TarefasUFSC/Sunchaser-Solar_Charging_System/Documentação/Diagramas/alto_nivel_comentado.jpg

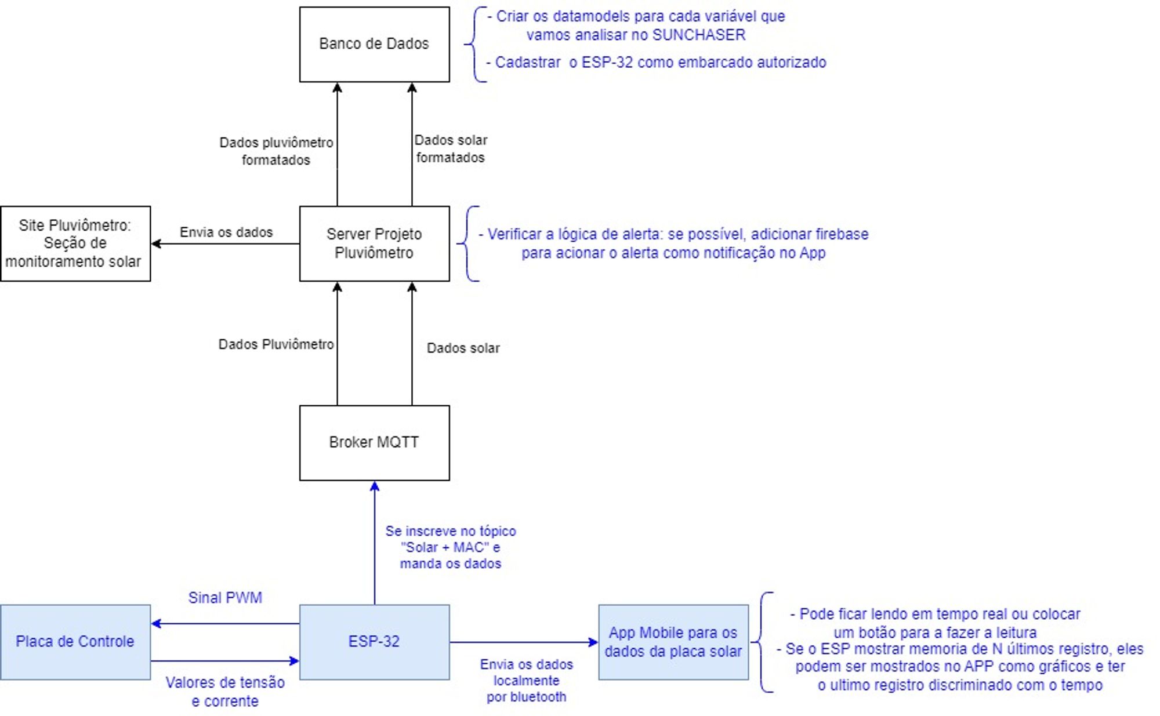
Documentação/Diagramas/alto_nivel_comentado.jpg
