TarefasUFSC/Sunchaser-Solar_Charging_System/Documentação/Diagramas/circuito_eletrico_reguladores.png

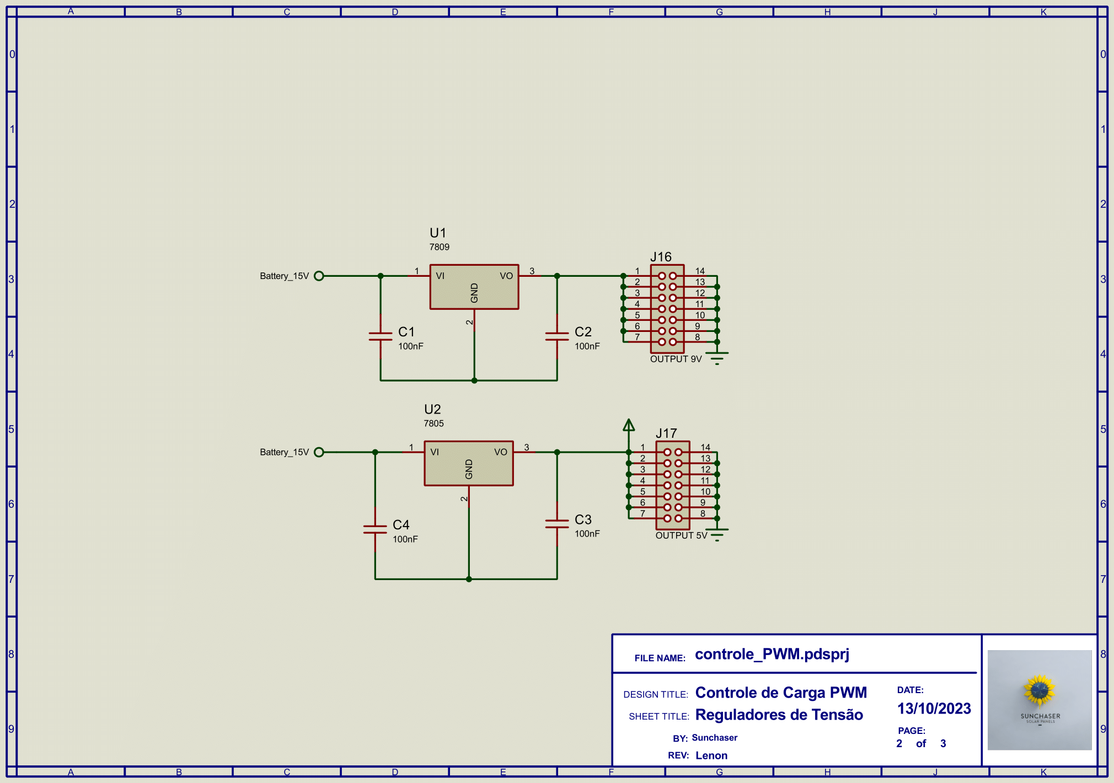
Documentação/Diagramas/circuito_eletrico_reguladores.png
