TarefasUFSC/Sunchaser-Solar_Charging_System/Documentação/Diagramas/circuito_eletrico_sensores.png

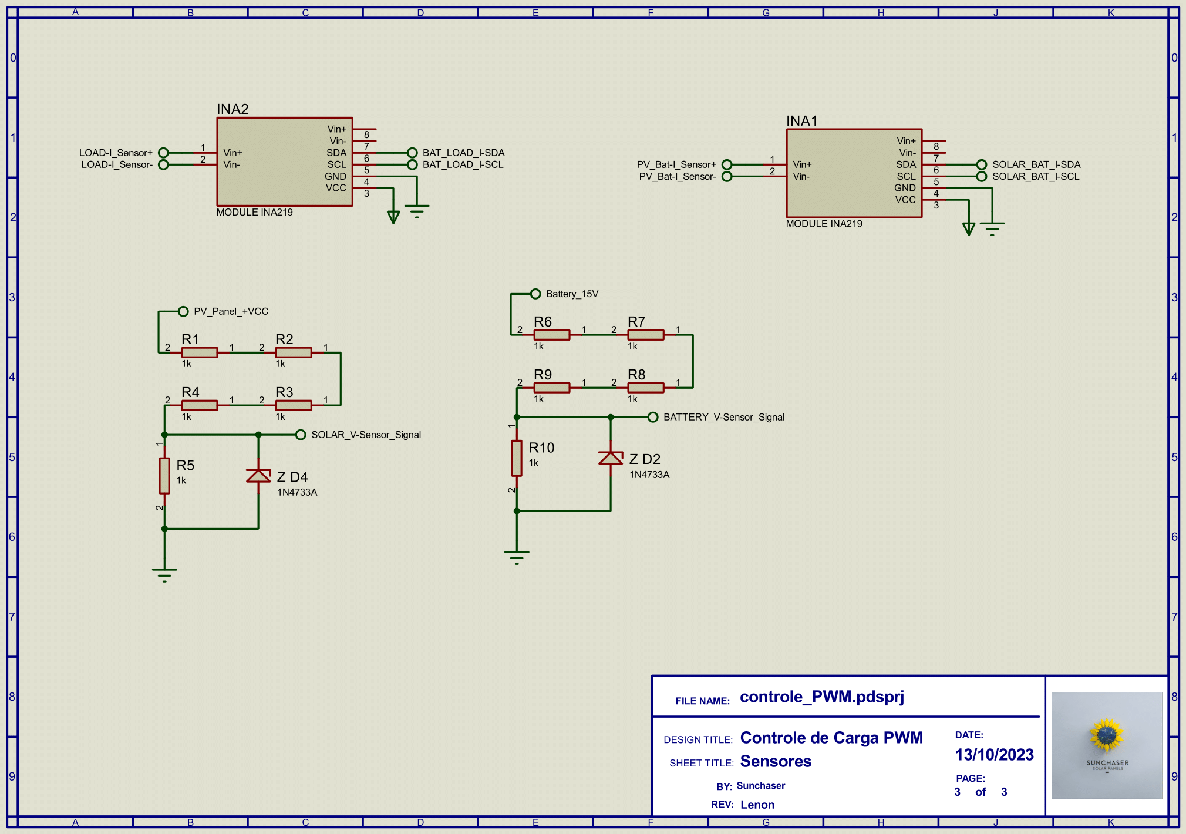
Documentação/Diagramas/circuito_eletrico_sensores.png
