TarefasUFSC/Sunchaser-Solar_Charging_System/Documentação/Diagramas/fluxograma_esp.png

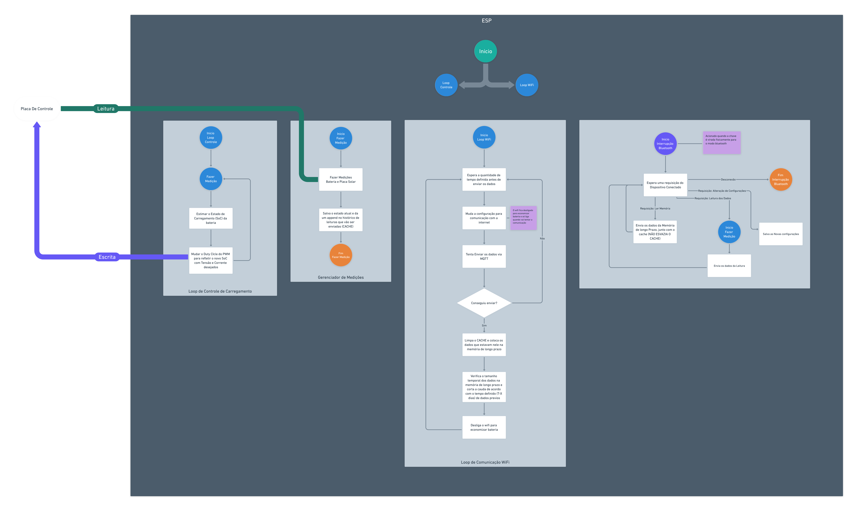
Documentação/Diagramas/fluxograma_esp.png
