TarefasUFSC/Sunchaser-Solar_Charging_System/Documentação/Diagramas/pcb_controle_do_switch_da_carga.png

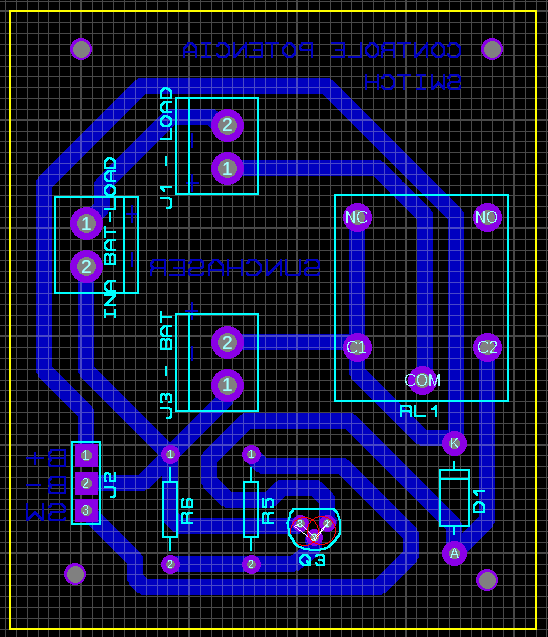
Documentação/Diagramas/pcb_controle_do_switch_da_carga.png
