TarefasUFSC/Sunchaser-Solar_Charging_System/Documentação/Diagramas/pcb_da_placa_do_esp_e_sensores.png

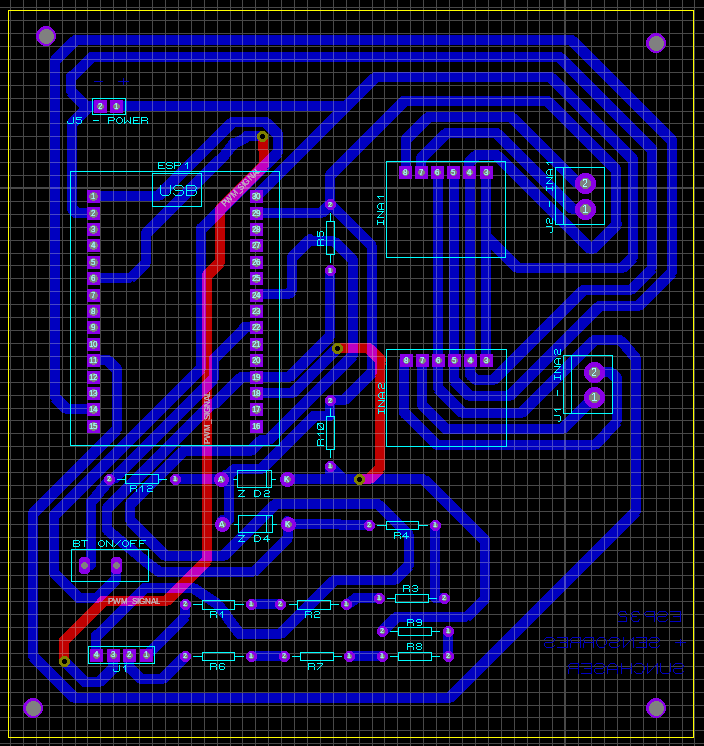
Documentação/Diagramas/pcb_da_placa_do_esp_e_sensores.png
