TarefasUFSC/Sunchaser-Solar_Charging_System/Documentação/Diagramas/pcb_placa_all.png

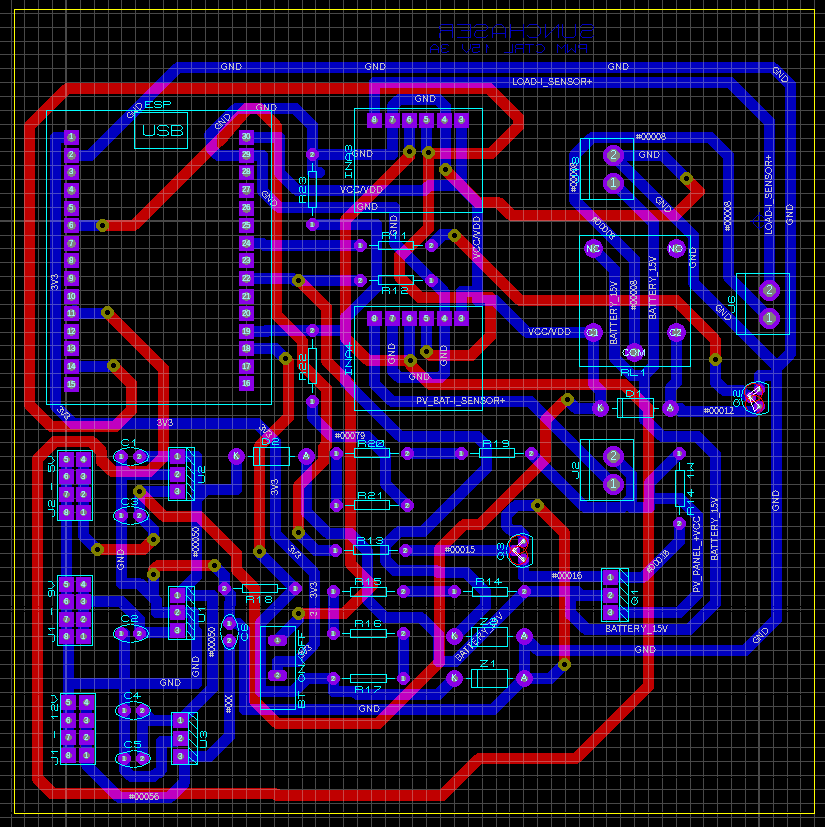
Documentação/Diagramas/pcb_placa_all.png
