TarefasUFSC/Sunchaser-Solar_Charging_System/Documentação/Diagramas/pcb_placa_de_controle_pwm.png

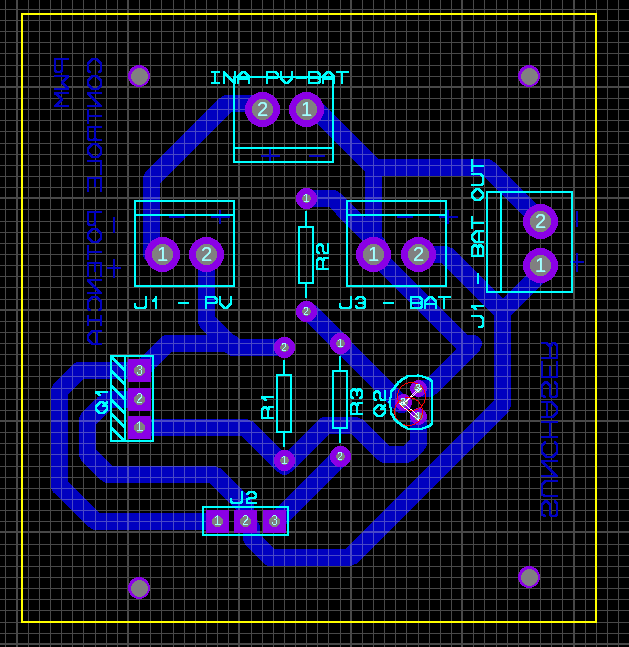
Documentação/Diagramas/pcb_placa_de_controle_pwm.png
