TarefasUFSC/Sunchaser-Solar_Charging_System/Documentação/Diagramas/pcb_reguladores.png

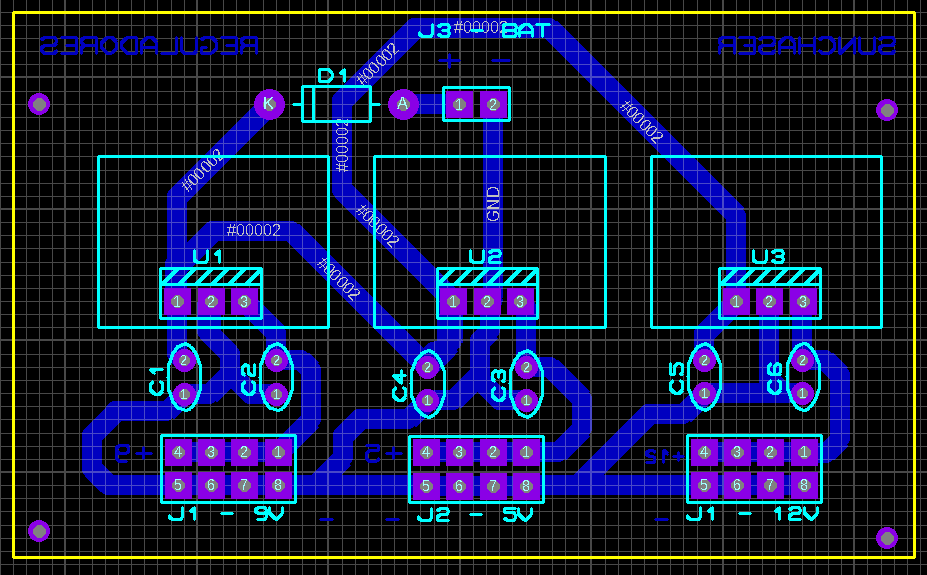
Documentação/Diagramas/pcb_reguladores.png
