TarefasUFSC/Sunchaser-Solar_Charging_System/Documentação/Diagramas/tela1.png

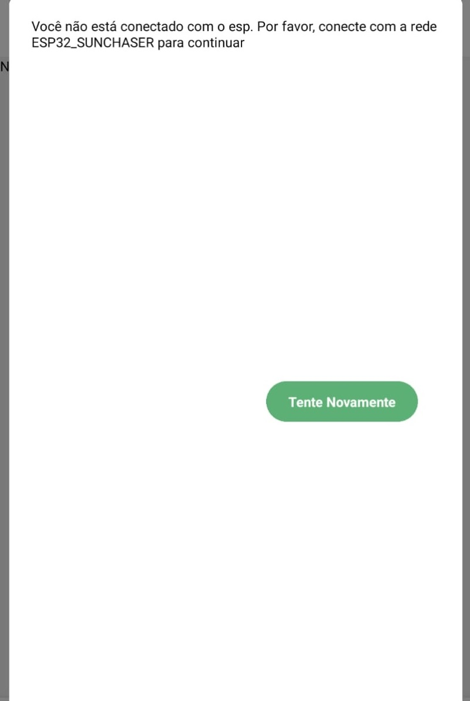
Documentação/Diagramas/tela1.png
