TarefasUFSC/Sunchaser-Solar_Charging_System/Documentação/Diagramas/tela2.png

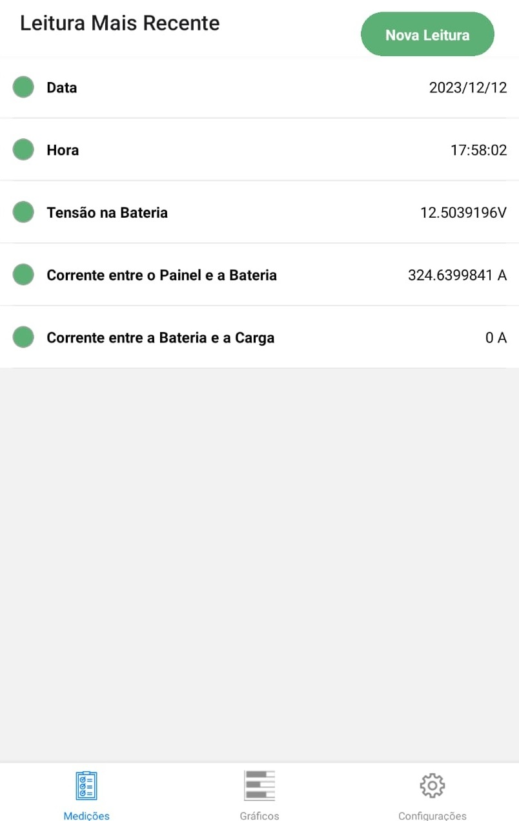
Documentação/Diagramas/tela2.png
