TarefasUFSC/Sunchaser-Solar_Charging_System/Documentação/Diagramas/tela3.png

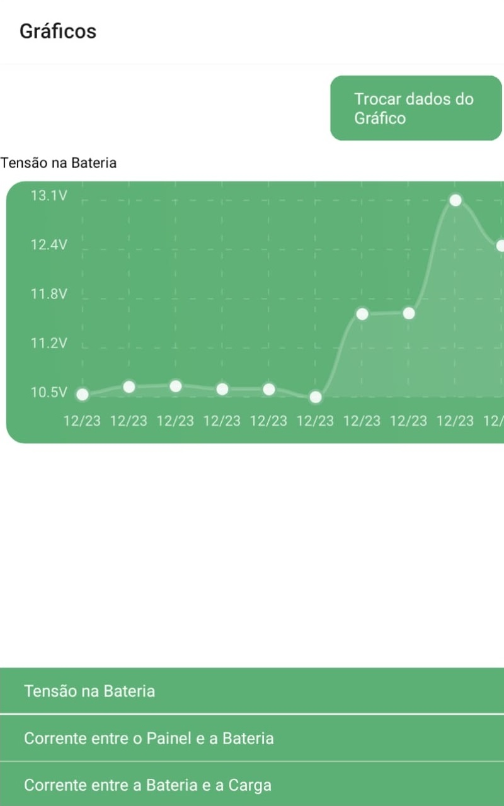
Documentação/Diagramas/tela3.png
