TarefasUFSC/Sunchaser-Solar_Charging_System/Placa de Controle/Controle de Carga PWM/hardware proteus 8.9/PCB/circuito-top_coppper.PDF

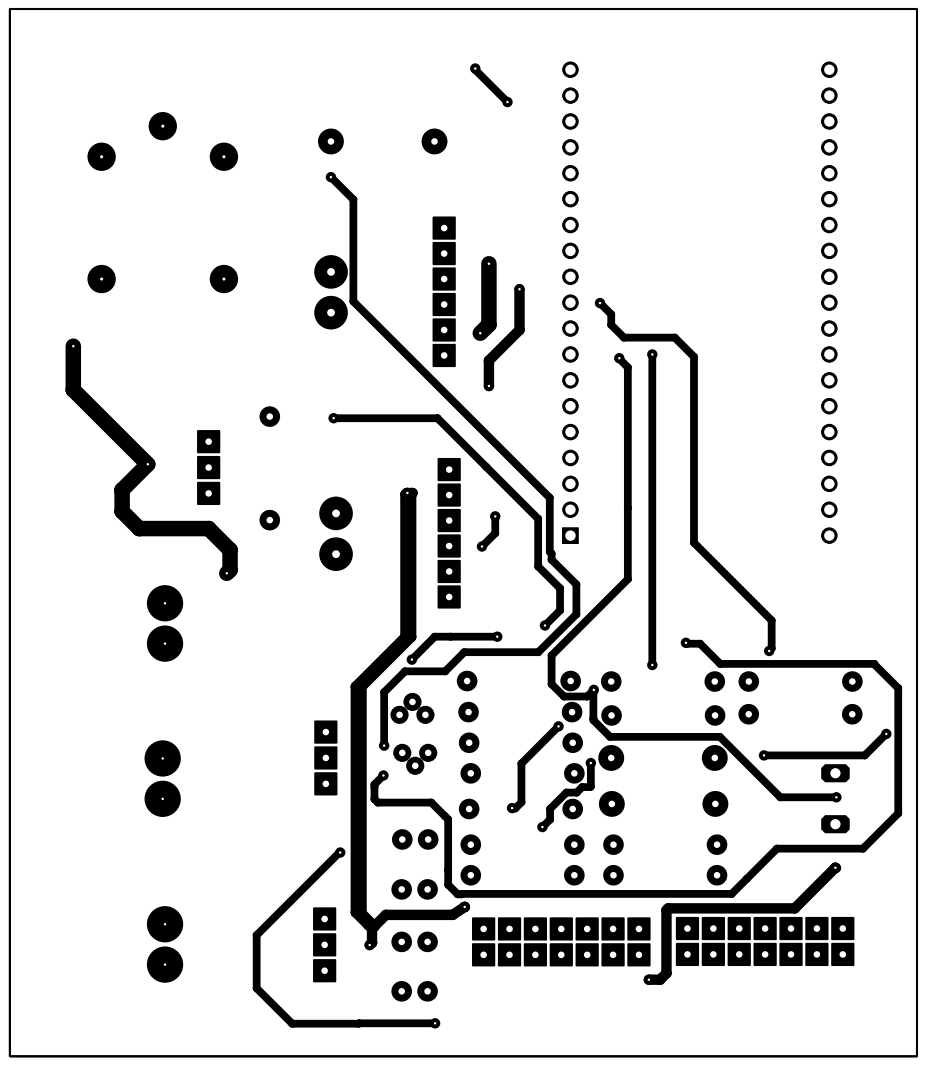
[picture p67: page 1]
