TarefasUFSC/Sunchaser-Solar_Charging_System/Placa de Controle/Controle de Carga PWM/hardware_sep_by_function/controle_de_pot-PWM/pcb/BOTTOM_COPPER_PWM.pdf

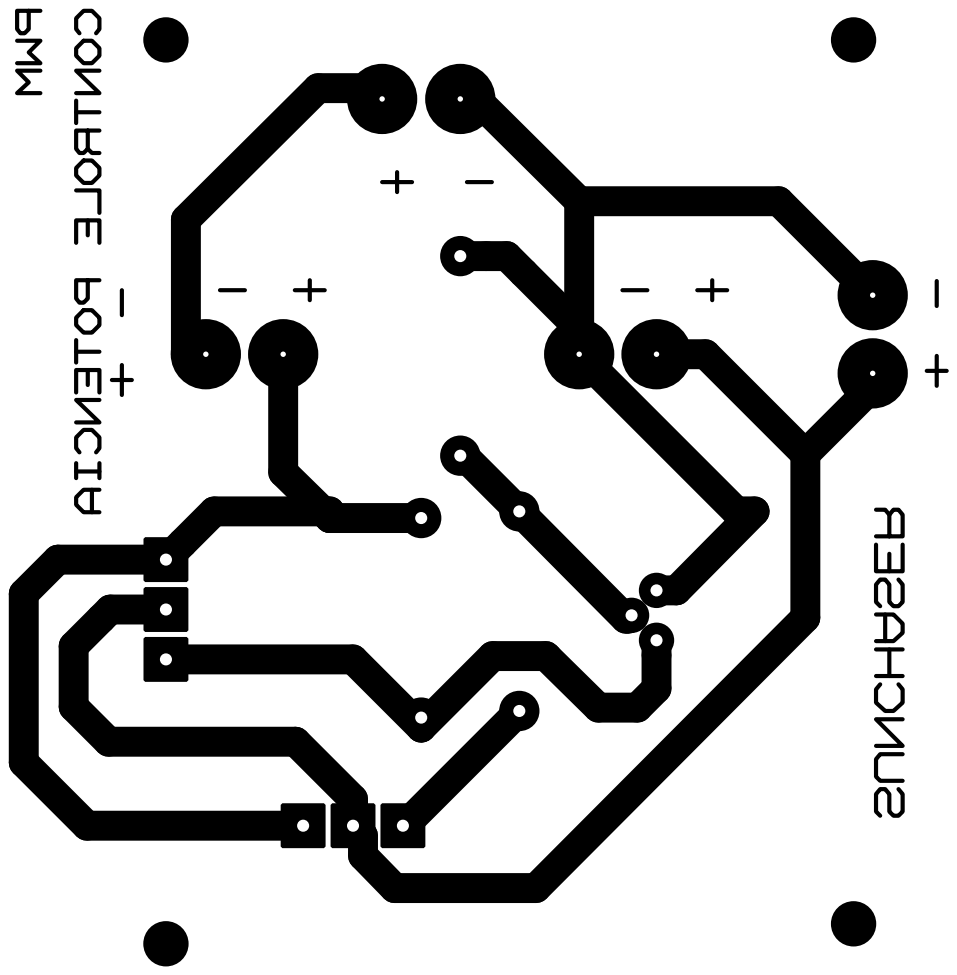
[picture p68: page 1]
