TarefasUFSC/Sunchaser-Solar_Charging_System/Placa de Controle/Controle de Carga PWM/hardware_sep_by_function/controle_de_pot-PWM/pcb/TOP_SILK_PWM.pdf

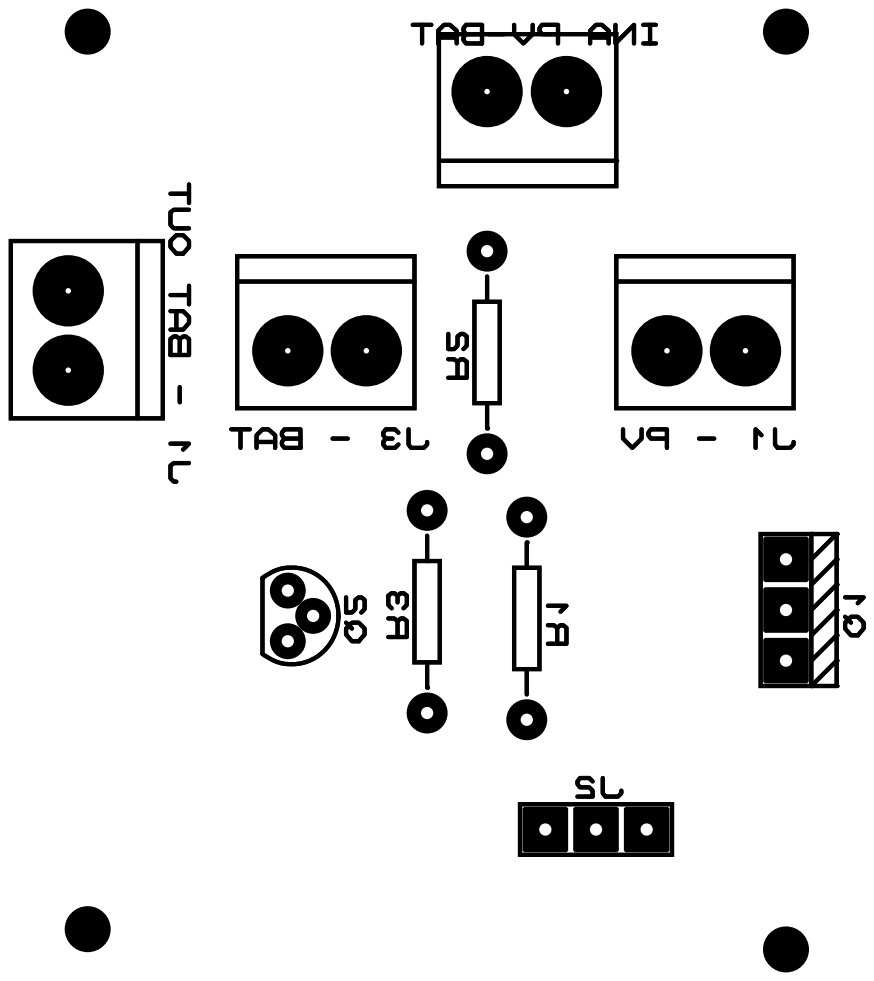
[picture p69: page 1]
