TarefasUFSC/Sunchaser-Solar_Charging_System/Placa de Controle/Controle de Carga PWM/hardware_sep_by_function/controle_de_pot-SWITCH/pcb/bottom_copper_SWITCH.pdf

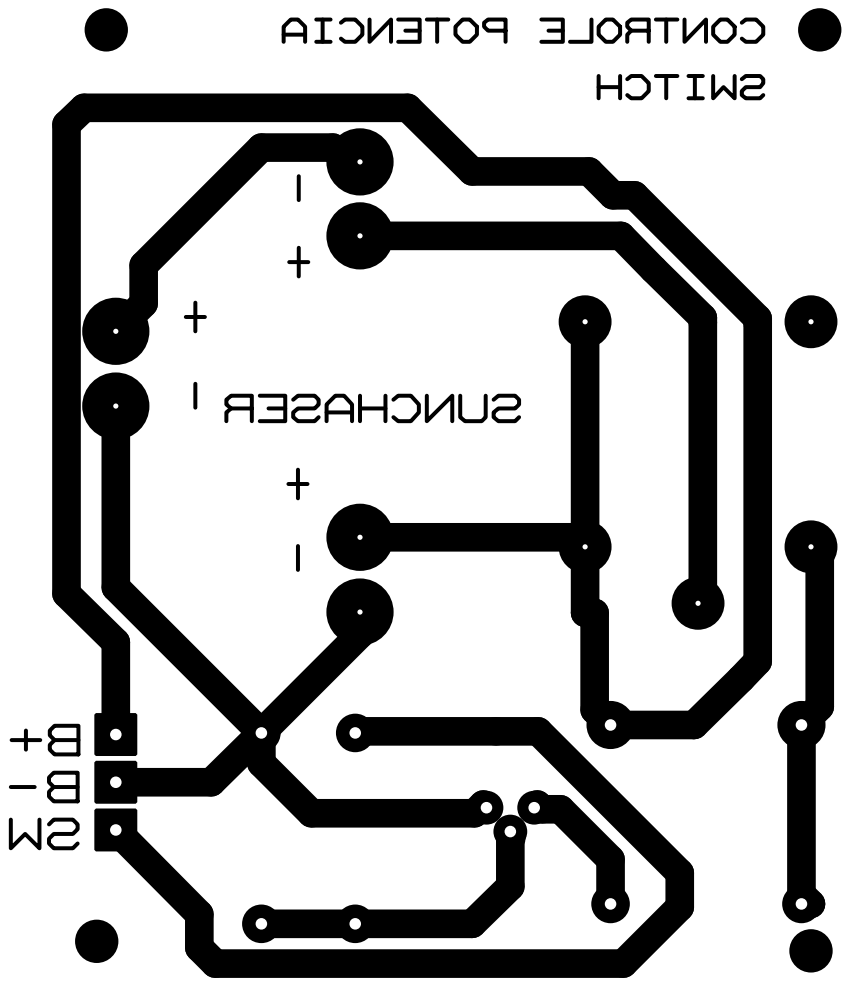
[picture p70: page 1]
