TarefasUFSC/Sunchaser-Solar_Charging_System/Placa de Controle/Controle de Carga PWM/hardware_sep_by_function/controle_de_pot-SWITCH/pcb/top_silk_SWITCH.pdf

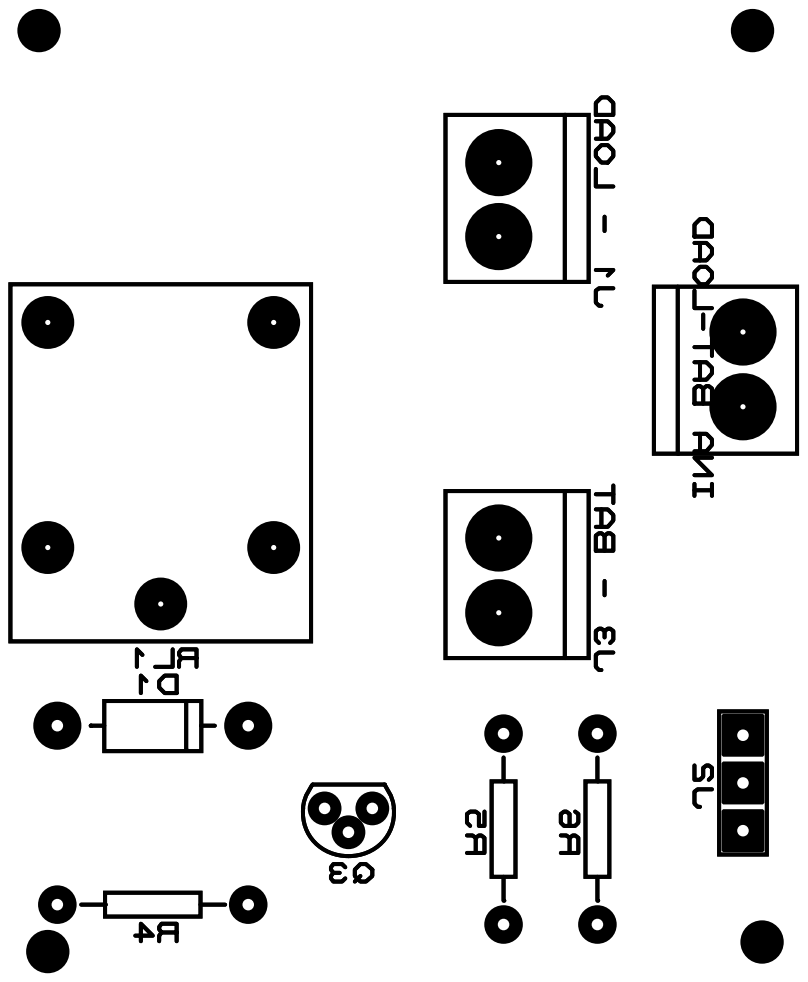
[picture p71: page 1]
