TarefasUFSC/Sunchaser-Solar_Charging_System/Placa de Controle/Controle de Carga PWM/hardware_sep_by_function/controle_de_pot/pcb/bottom_copper_controle.pdf

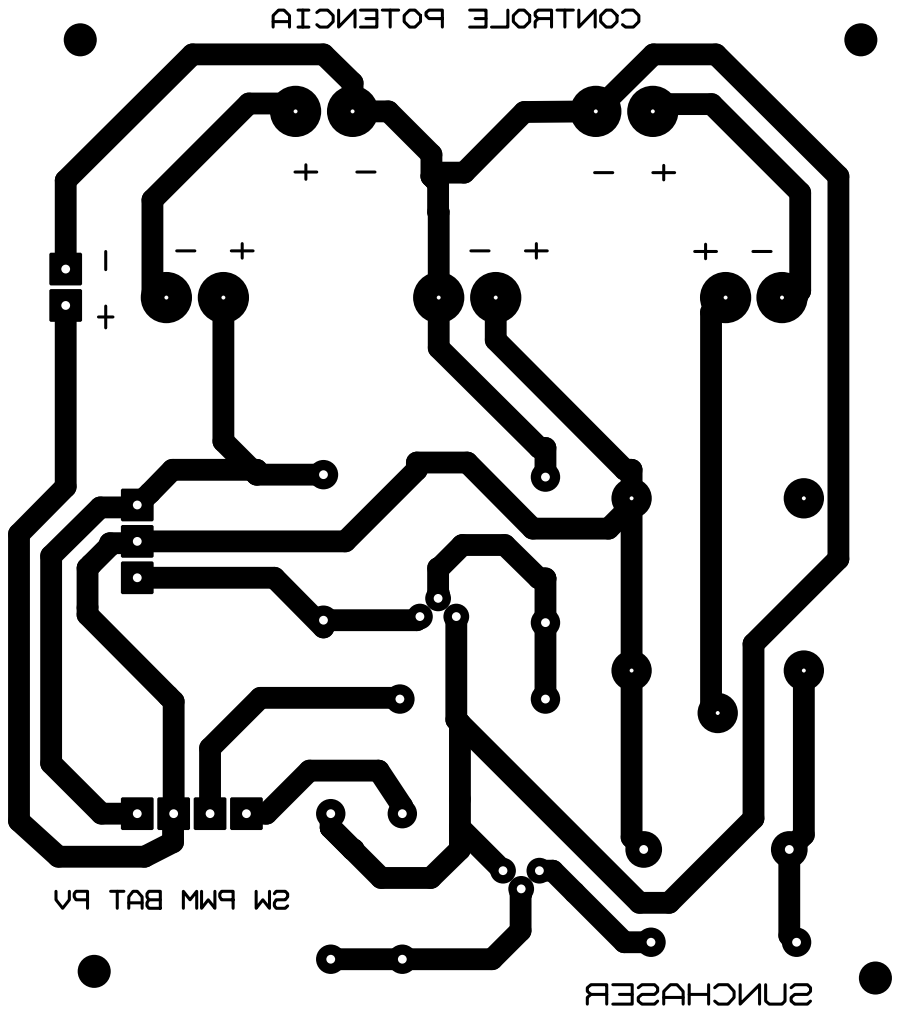
[picture p72: page 1]
