TarefasUFSC/Sunchaser-Solar_Charging_System/Placa de Controle/Controle de Carga PWM/hardware_sep_by_function/controle_de_pot/pcb/top_silk_controle.pdf

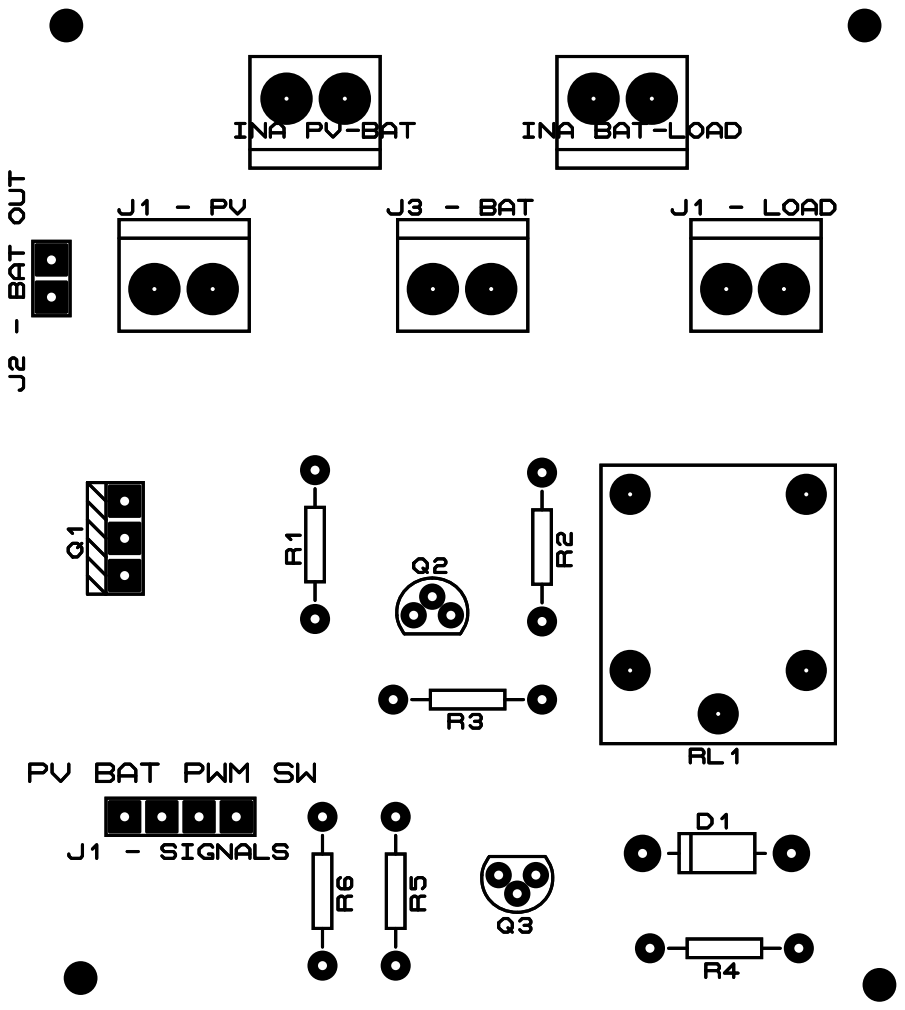
[picture p73: page 1]
