TarefasUFSC/Sunchaser-Solar_Charging_System/Placa de Controle/Controle de Carga PWM/hardware_sep_by_function/esp_and_sensors/pcb/esp_and_sensors_bottom_copper.pdf

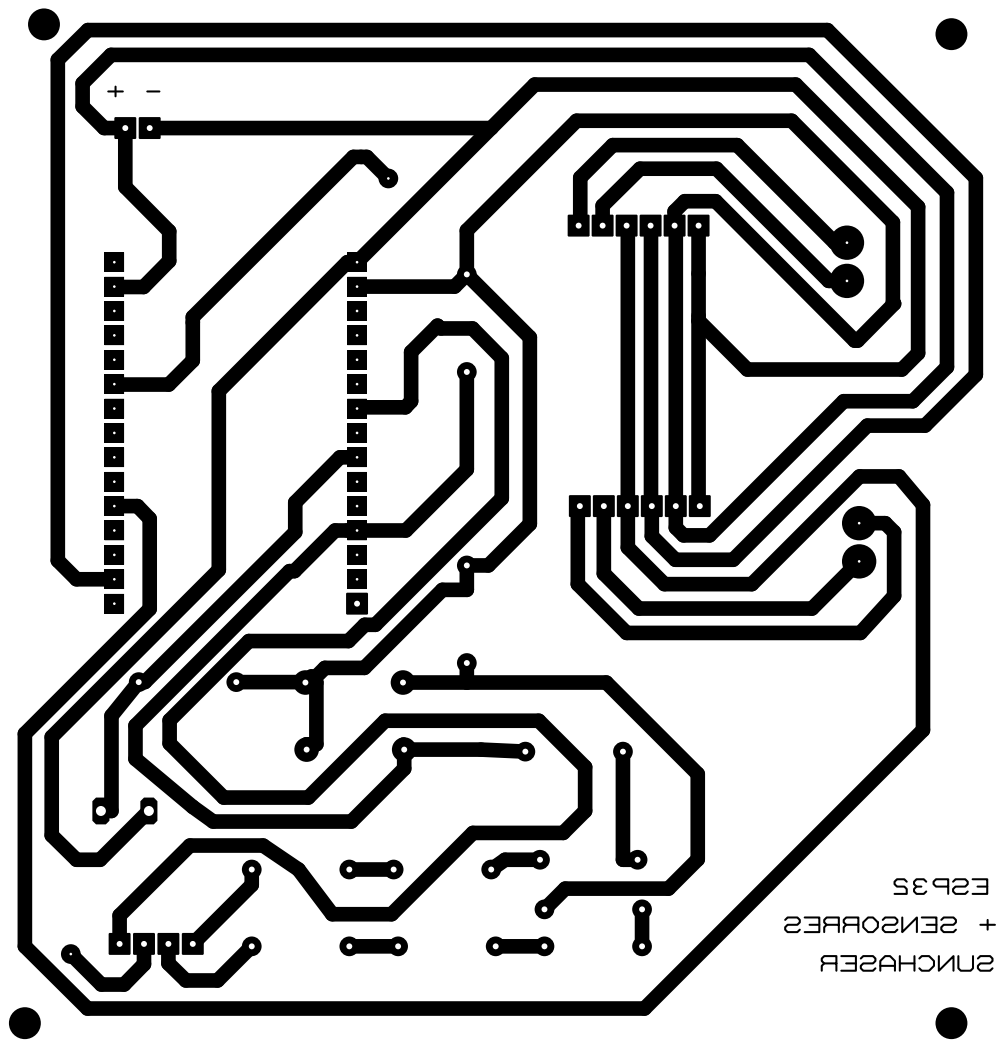
[picture p74: page 1]
