TarefasUFSC/Sunchaser-Solar_Charging_System/Placa de Controle/Controle de Carga PWM/hardware_sep_by_function/esp_and_sensors/pcb/esp_and_sensors_top_silk_and_coopper.pdf

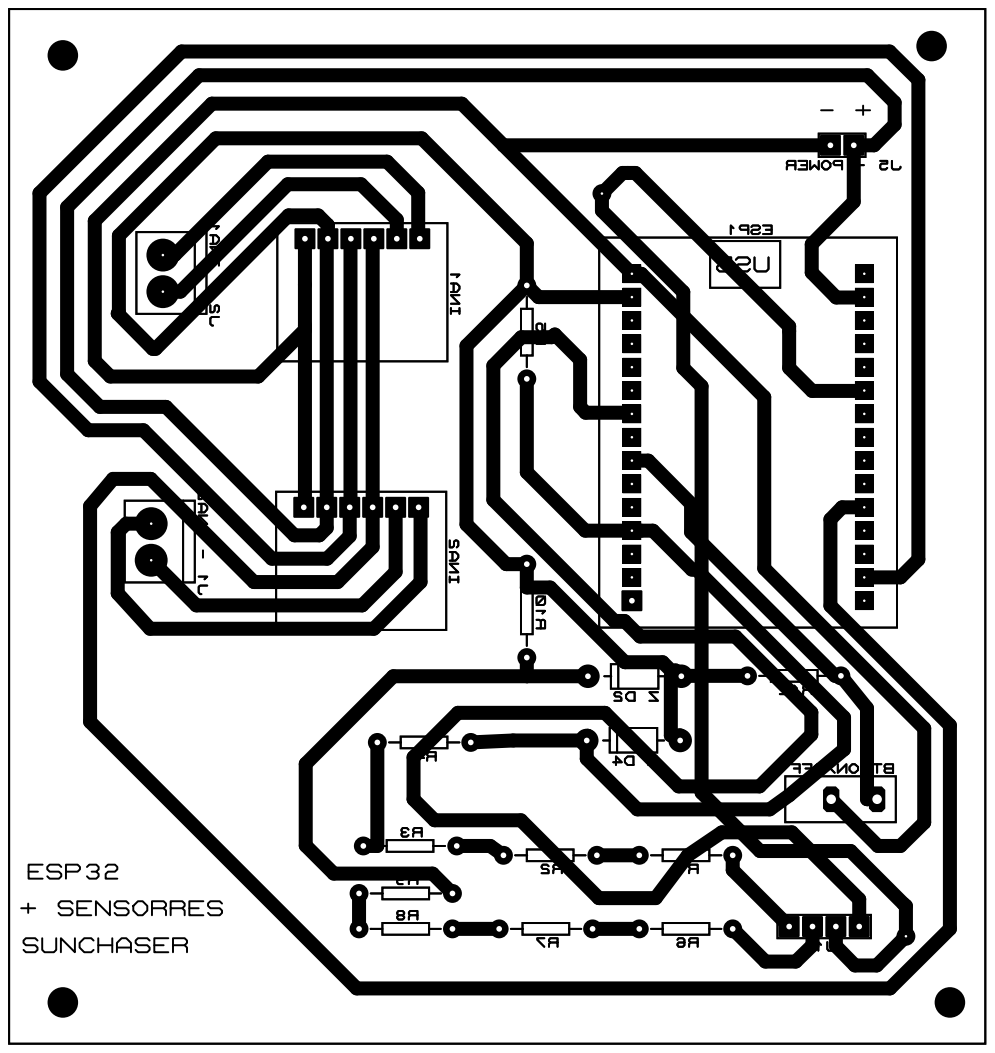
[picture p75: page 1]
