TarefasUFSC/Sunchaser-Solar_Charging_System/Placa de Controle/Controle de Carga PWM/hardware_sep_by_function/reguladores_de_tensao/pcb/reguladores_top_silk.pdf

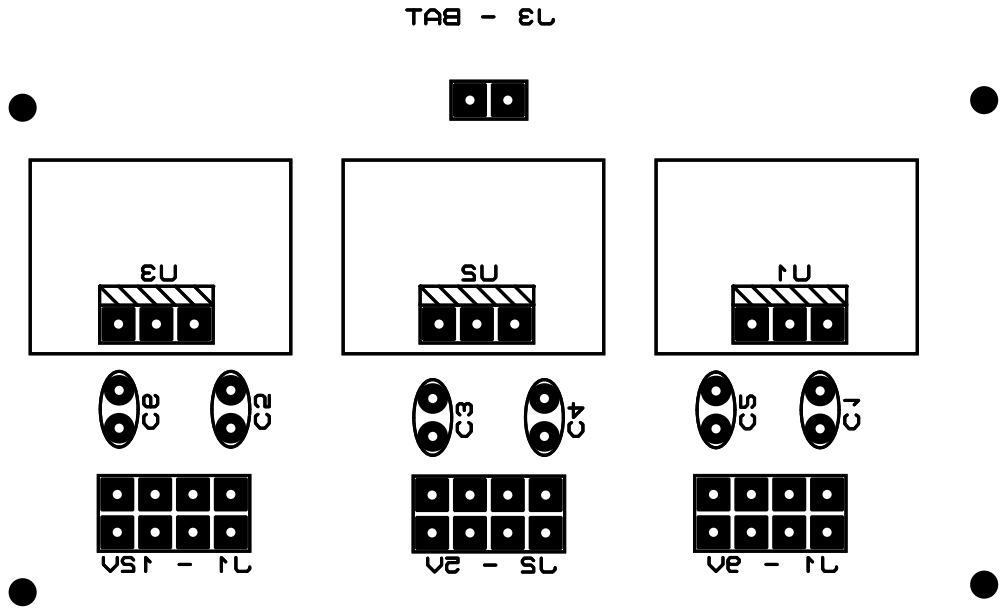
[picture p77: page 1]
