TarefasUFSC/Sunchaser-Solar_Charging_System/Programas ESP/Desenvolvimento/7-BLE_server/7-BLE_server.ino

#include "BLE_Server.h"

void setup() {
  Serial.begin(115200);
  BLE_init();

  pCharacteristic->setValue("Hello World!");
  pService->start();
  //BLEAdvertising *pAdvertising = pServer->getAdvertising();  // this still is working for backward compatibility
  BLEAdvertising *pAdvertising = BLEDevice::getAdvertising();
  pAdvertising->addServiceUUID(SERVICE_UUID);
  pAdvertising->setScanResponse(true);
  pAdvertising->setMinPreferred(0x06);  // functions that help with iPhone connections issue
  pAdvertising->setMinPreferred(0x12);
  BLEDevice::startAdvertising();
  Serial.println("Characteristic defined! Now you can read it in your phone!");
}

void loop() {
  delay(2000);
}
