TarefasUFSC/Sunchaser-Solar_Charging_System/Programas ESP/ProgramaFinal/communicator.cpp

#include "communicator.h"
#include "SaveToFlash.h"
Communicator::Communicator() : _web_server(80), _mqtt_client(_esp_client) // Changed: Initialize _web_server here
{
}

void Communicator::init(SaveToFlash *files, TimeConfigurations *configs, BatteryControl *battery_controller)
{
  
  this->_battery_controller = battery_controller;
  this->_files = files;
  this->_setup_wifi_client();
  this->attach_interruption();

  this->mac_address = WiFi.macAddress();
  Serial.print("MAC Cliente: ");
  Serial.println(this->mac_address);

  this->_time_configs = configs;
}

bool Communicator::isServer()
{
  return this->is_server;
}
