TarefasUFSC/Sunchaser-Solar_Charging_System/Programas ESP/Desenvolvimento/7-BLE_server/BLE_Server.cpp

#include "BLE_Server.h"

void BLE_init(){
    Serial.println("Starting BLE work!");

    BLEDevice::init("Sunchaser ESP-32 BLE");
    BLEServer *pServer = BLEDevice::createServer();
    BLEService *pService = pServer->createService(SERVICE_UUID);
    BLECharacteristic *pCharacteristic = pService->createCharacteristic(
                                         CHARACTERISTIC_UUID,
                                         BLECharacteristic::PROPERTY_READ |
                                         BLECharacteristic::PROPERTY_WRITE
                                       );
}
